Taras-Burko/-V.A.W_Monitor/Panel_3D_Model/IMG_2704.jpeg

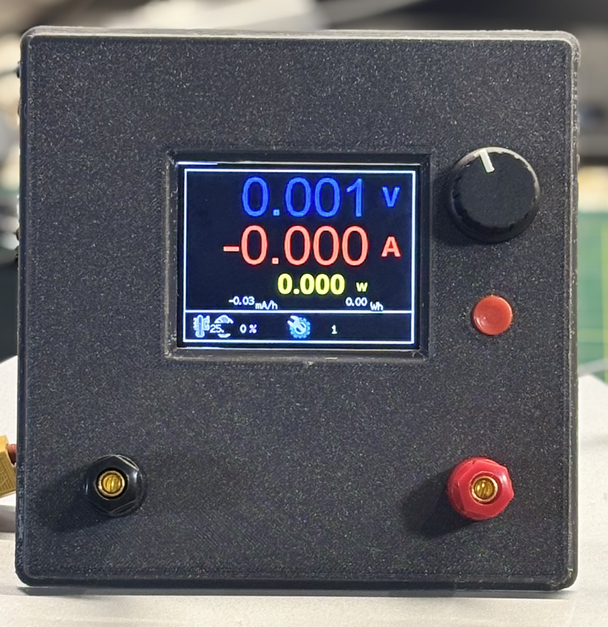
Panel_3D_Model/IMG_2704.jpeg
