Taras-Burko/-V.A.W_Monitor/Panel_3D_Model/IMG_2706.jpeg

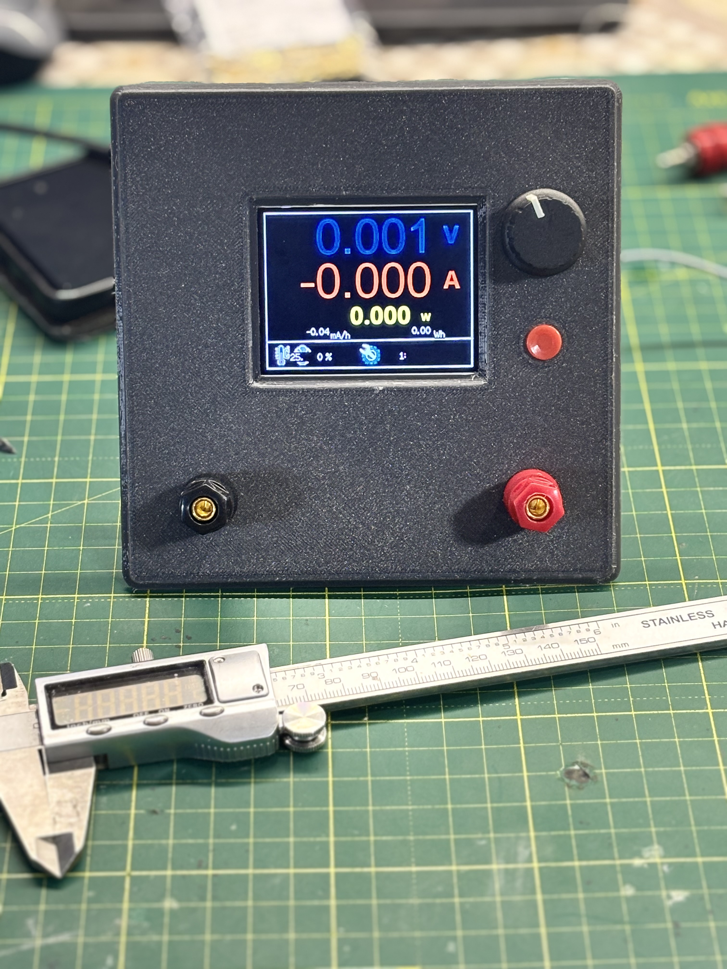
Panel_3D_Model/IMG_2706.jpeg
