Taras-Burko/-V.A.W_Monitor/Sketch/PNG_file.h

const unsigned short fan_image[0x384] PROGMEM ={
0x0000, 0x0000, 0x0000, 0x0000, 0x0000, 0x0000, 0x0000, 0x0000, 0x0000, 0x0000, 0x0000, 0x0000, 0x0000, 0xF79E, 0xFFFF, 0xFFDF,   // 0x0010 (16)
0xFFFF, 0xFFFF, 0x7BEF, 0x0000, 0x0000, 0x0000, 0x0000, 0x0000, 0x0000, 0x0000, 0x0000, 0x0000, 0x0000, 0x0000, 0x0000, 0x0000,   // 0x0020 (32)
0x0000, 0x0000, 0x0000, 0x0000, 0x0000, 0x0000, 0x0000, 0x0000, 0x0000, 0xC618, 0xFFDF, 0xE73C, 0xE71C, 0xDEFB, 0xDEFB, 0xE71C,   // 0x0030 (48)
0xF79E, 0xFFDF, 0x0000, 0x0000, 0x0000, 0x0000, 0x0000, 0x0000, 0x0000, 0x0000, 0x0000, 0x0000, 0x0000, 0x0000, 0x0000, 0x0000,   // 0x0040 (64)
0x0000, 0x0000, 0x0000, 0x0000, 0x0000, 0x0000, 0xDEDB, 0xF7BE, 0xDEFB, 0x9CF3, 0x94B2, 0x94B2, 0x94B2, 0x94B2, 0xA534, 0xEF5D,   // 0x0050 (80)
0xFFFF, 0x0000, 0x0000, 0x0000, 0x0000, 0x0000, 0x0000, 0x0000, 0x0000, 0x0000, 0x0000, 0x0000, 0x0000, 0x0000, 0x0000, 0x0000,   // 0x0060 (96)
0x0000, 0x0000, 0xDEDB, 0xEF7D, 0xF7BE, 0xE71C, 0x9492, 0x9CF3, 0x9CF3, 0x9CF3, 0x9CF3, 0x9CF3, 0x9CD3, 0x7BEF, 0xEF5D, 0xFFDF,   // 0x0070 (112)
0x0000, 0x0000, 0x0000, 0x0000, 0x0000, 0x0000, 0x0000, 0x0000, 0x0000, 0x0000, 0x0000, 0x0000, 0x0000, 0x0000, 0x0000, 0xEF5D,   // 0x0080 (128)
0xF7BE, 0xEF7D, 0xF7BE, 0xC638, 0x94B2, 0x9CF3, 0x9CF3, 0x9CF3, 0x9CF3, 0x9CF3, 0xA514, 0x94B2, 0x8410, 0xEF7D, 0xF7BE, 0xAD55,   // 0x0090 (144)
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
0x049C, 0xFF98, 0xFFFF, 0xF7BE, 0x0000, 0x0000, 0x0000, 0x0000, 0x0000, 0x0000, 0xEF7D, 0xFFFF, 0xFFFF, 0xFFFF, 0xFFFF, 0xF79E,   // 0x0270 (624)
0x0000, 0x04FC, 0x05BF, 0x051D, 0x0000, 0x0000, 0x0000, 0x0000, 0x0000, 0x0000, 0x051C, 0x053D, 0x057E, 0x055E, 0x051C, 0x0000,   // 0x0280 (640)
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
